ldab/iot_plant_watering_sensor_esp/include/secrets.h

const char* s_wifi_ssid     = "MY_WIFI_SSID";
const char* s_wifi_password = "PASSWORD";

const char* s_mqtt_server   = "s_mqtt_server";
const char* s_mqtt_user     = "s_mqtt_user";
const char* s_mqtt_pass     = "s_mqtt_pass";
uint16_t    s_mqtt_port     = 1883;
